mod-audio/cc-hw-arduino-shield/cases/distance/mod-arduino-shield-case-distance.sch

## KiCad design cases/distance/mod-arduino-shield-case-distance.sch (2014-12-04)

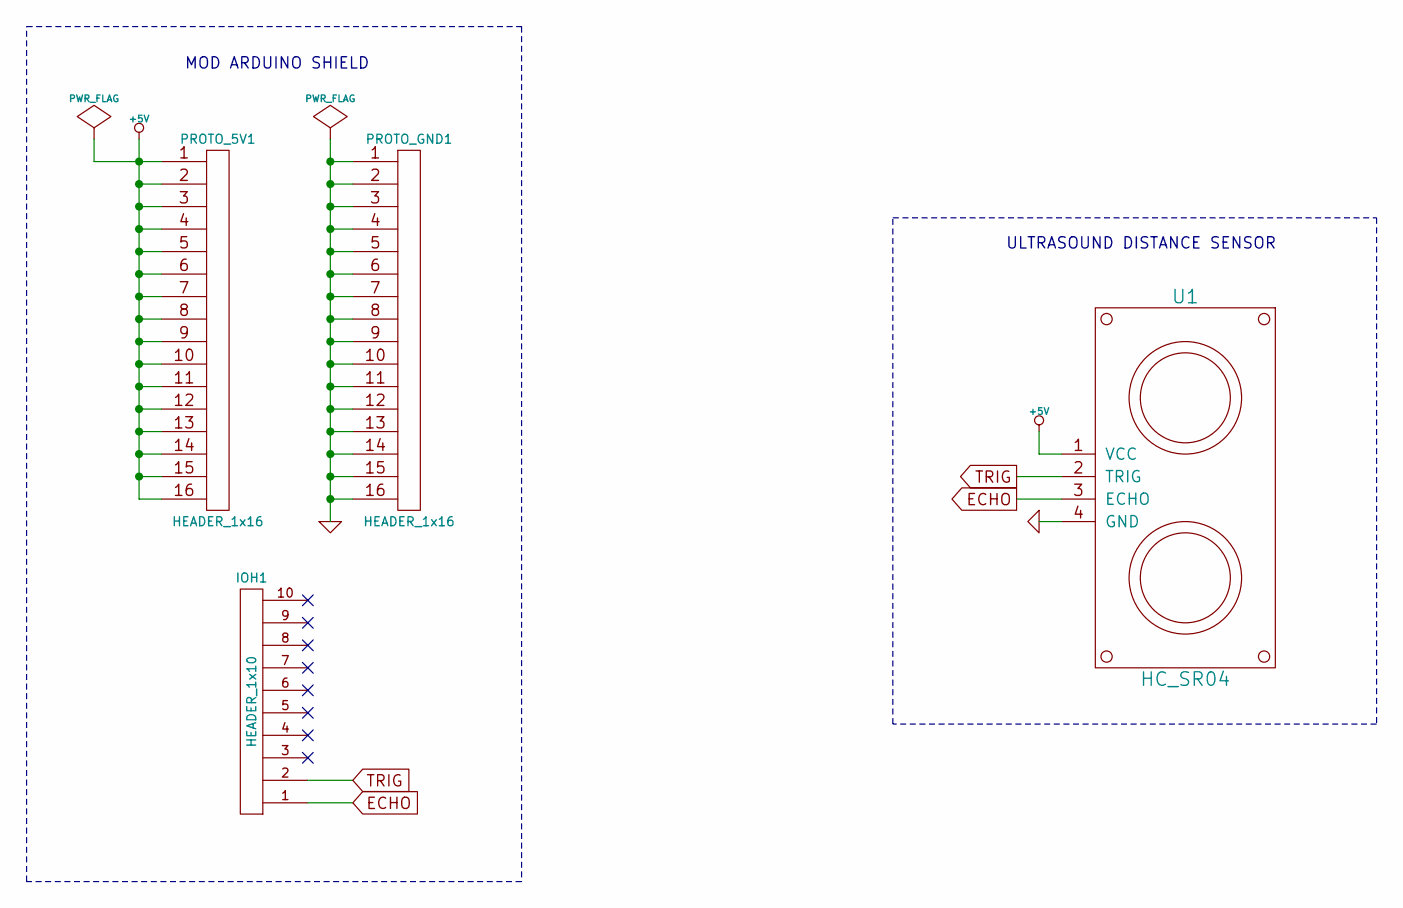
[picture p15: schematic mod-arduino-shield-case-distance.sch]

Parts:
IOH1: HEADER_1x10
PROTO_5V1: HEADER_1x16
PROTO_GND1: HEADER_1x16
U1: HC_SR04

Connections:
+5V: PROTO_5V1.1, PROTO_5V1.2, PROTO_5V1.3, PROTO_5V1.4, PROTO_5V1.5, PROTO_5V1.6, PROTO_5V1.7, PROTO_5V1.8, PROTO_5V1.9, PROTO_5V1.10, PROTO_5V1.11, PROTO_5V1.12, PROTO_5V1.13, PROTO_5V1.14, PROTO_5V1.15, PROTO_5V1.16, U1.1 (VCC)
ECHO: IOH1.1, U1.3 (ECHO)
GND: PROTO_GND1.1, PROTO_GND1.2, PROTO_GND1.3, PROTO_GND1.4, PROTO_GND1.5, PROTO_GND1.6, PROTO_GND1.7, PROTO_GND1.8, PROTO_GND1.9, PROTO_GND1.10, PROTO_GND1.11, PROTO_GND1.12, PROTO_GND1.13, PROTO_GND1.14, PROTO_GND1.15, PROTO_GND1.16, U1.4 (GND)
TRIG: IOH1.2, U1.2 (TRIG)

Notes on the sheet:
ULTRASOUND DISTANCE SENSOR
MOD ARDUINO SHIELD
