mod-audio/cc-hw-arduino-shield/cases/expression-pedal/mod-arduino-shield-case-expression-pedal.sch

## KiCad design cases/expression-pedal/mod-arduino-shield-case-expression-pedal.sch (2014-12-04)

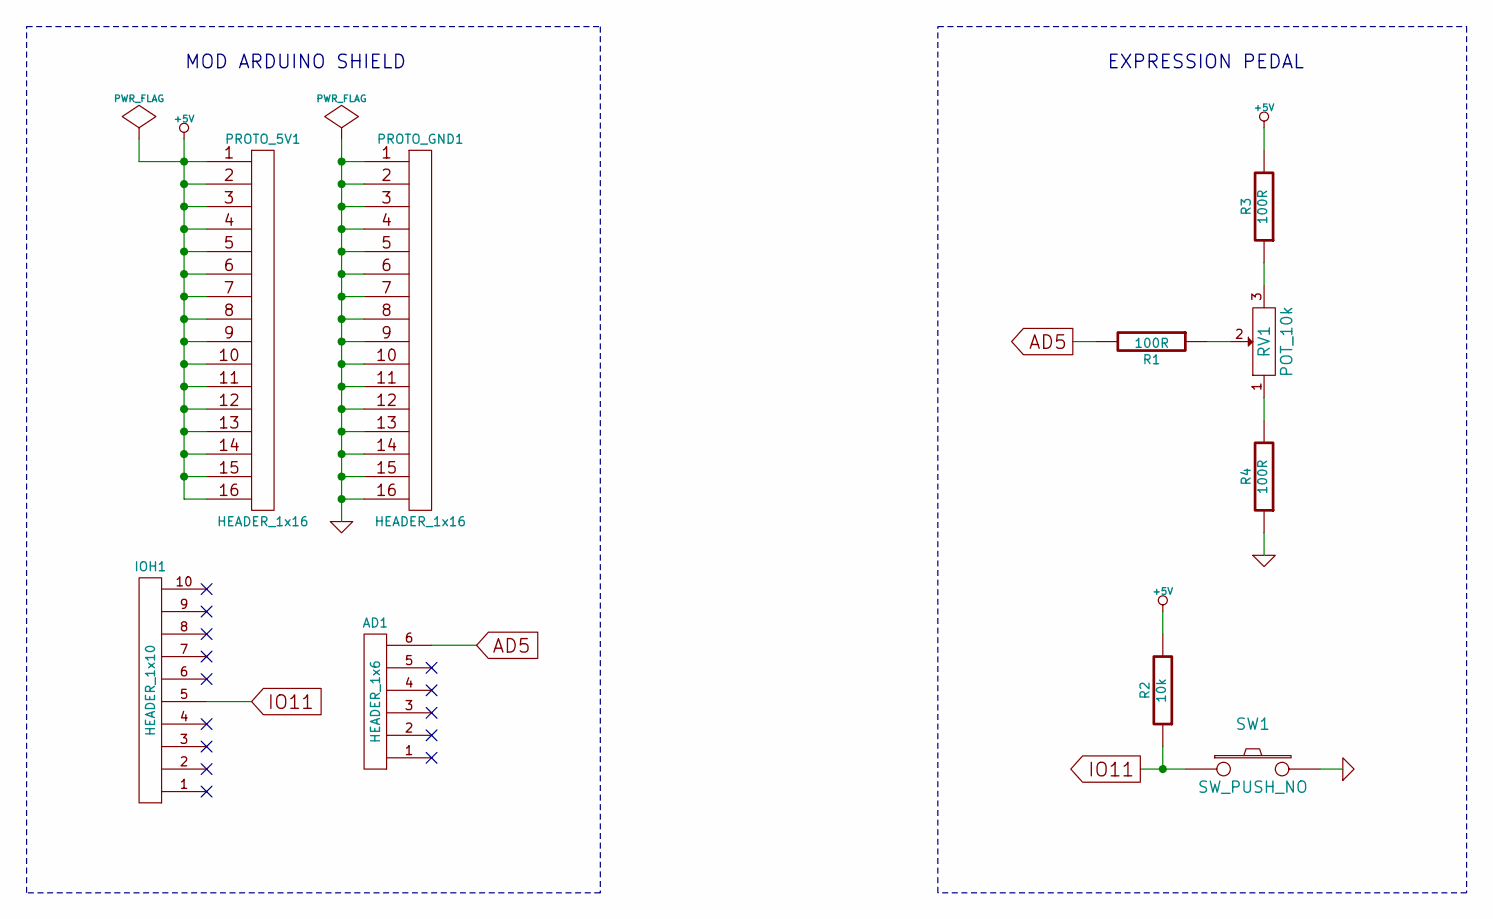
[picture p16: schematic mod-arduino-shield-case-expression-pedal.sch]

Parts:
AD1: HEADER_1x6
IOH1: HEADER_1x10
PROTO_5V1: HEADER_1x16
PROTO_GND1: HEADER_1x16
R1, R3, R4: 100R
R2: 10k
RV1: POT_10k
SW1: SW_PUSH_NO

Connections:
+5V: PROTO_5V1.1, PROTO_5V1.2, PROTO_5V1.3, PROTO_5V1.4, PROTO_5V1.5, PROTO_5V1.6, PROTO_5V1.7, PROTO_5V1.8, PROTO_5V1.9, PROTO_5V1.10, PROTO_5V1.11, PROTO_5V1.12, PROTO_5V1.13, PROTO_5V1.14, PROTO_5V1.15, PROTO_5V1.16, R2.2, R3.2
AD5: AD1.6, R1.2
GND: PROTO_GND1.1, PROTO_GND1.2, PROTO_GND1.3, PROTO_GND1.4, PROTO_GND1.5, PROTO_GND1.6, PROTO_GND1.7, PROTO_GND1.8, PROTO_GND1.9, PROTO_GND1.10, PROTO_GND1.11, PROTO_GND1.12, PROTO_GND1.13, PROTO_GND1.14, PROTO_GND1.15, PROTO_GND1.16, R4.1, SW1.2
IO11: IOH1.5, R2.1, SW1.1
unnamed: R1.1, RV1.2
unnamed: R3.1, RV1.3
unnamed: R4.2, RV1.1

Notes on the sheet:
MOD ARDUINO SHIELD
EXPRESSION PEDAL
