mod-audio/cc-hw-arduino-shield/cases/footswitch/mod-arduino-shield-case-footswitch.sch

## KiCad design cases/footswitch/mod-arduino-shield-case-footswitch.sch (2014-12-04)

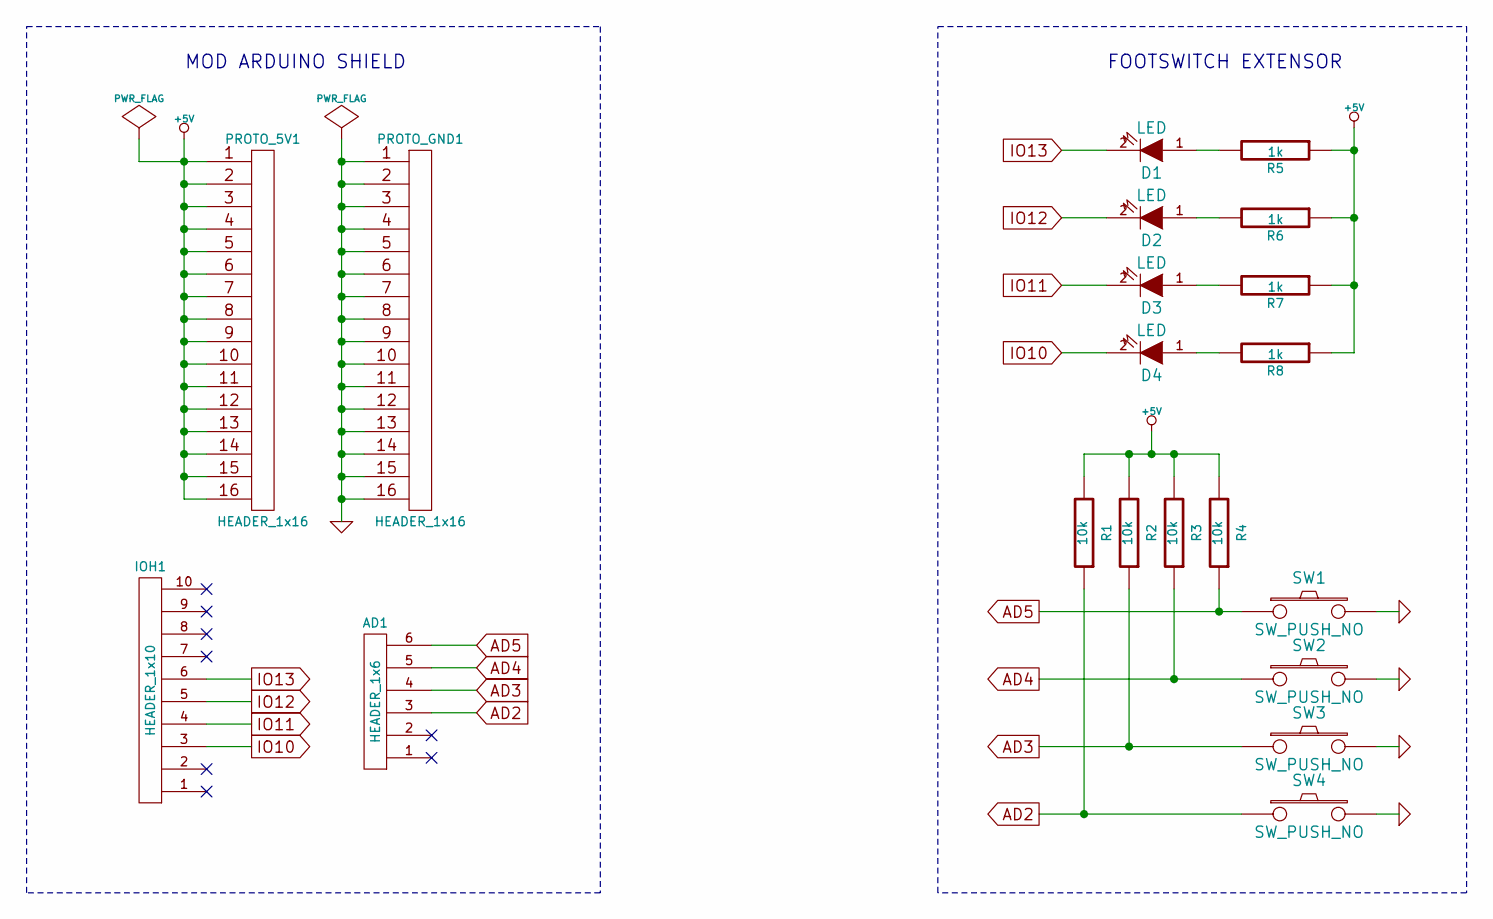
[picture p17: schematic mod-arduino-shield-case-footswitch.sch]

Parts:
AD1: HEADER_1x6
D1, D2, D3, D4: LED
IOH1: HEADER_1x10
PROTO_5V1: HEADER_1x16
PROTO_GND1: HEADER_1x16
R1, R2, R3, R4: 10k
R5, R6, R7, R8: 1k
SW1, SW2, SW3, SW4: SW_PUSH_NO

Connections:
+5V: PROTO_5V1.1, PROTO_5V1.2, PROTO_5V1.3, PROTO_5V1.4, PROTO_5V1.5, PROTO_5V1.6, PROTO_5V1.7, PROTO_5V1.8, PROTO_5V1.9, PROTO_5V1.10, PROTO_5V1.11, PROTO_5V1.12, PROTO_5V1.13, PROTO_5V1.14, PROTO_5V1.15, PROTO_5V1.16, R1.2, R2.2, R3.2, R4.2, R5.1, R6.1, R7.1, R8.1
AD2: AD1.3, R1.1, SW4.1
AD3: AD1.4, R2.1, SW3.1
AD4: AD1.5, R3.1, SW2.1
AD5: AD1.6, R4.1, SW1.1
GND: PROTO_GND1.1, PROTO_GND1.2, PROTO_GND1.3, PROTO_GND1.4, PROTO_GND1.5, PROTO_GND1.6, PROTO_GND1.7, PROTO_GND1.8, PROTO_GND1.9, PROTO_GND1.10, PROTO_GND1.11, PROTO_GND1.12, PROTO_GND1.13, PROTO_GND1.14, PROTO_GND1.15, PROTO_GND1.16, SW1.2, SW2.2, SW3.2, SW4.2
IO10: D4.2 (K), IOH1.3
IO11: D3.2 (K), IOH1.4
IO12: D2.2 (K), IOH1.5
IO13: D1.2 (K), IOH1.6
unnamed: D1.1 (A), R5.2
unnamed: D2.1 (A), R6.2
unnamed: D3.1 (A), R7.2
unnamed: D4.1 (A), R8.2

Notes on the sheet:
MOD ARDUINO SHIELD
FOOTSWITCH EXTENSOR
