mod-audio/cc-hw-arduino-shield/cases/ldr/mod-arduino-shield-case-ldr.sch

## KiCad design cases/ldr/mod-arduino-shield-case-ldr.sch (2014-12-04)

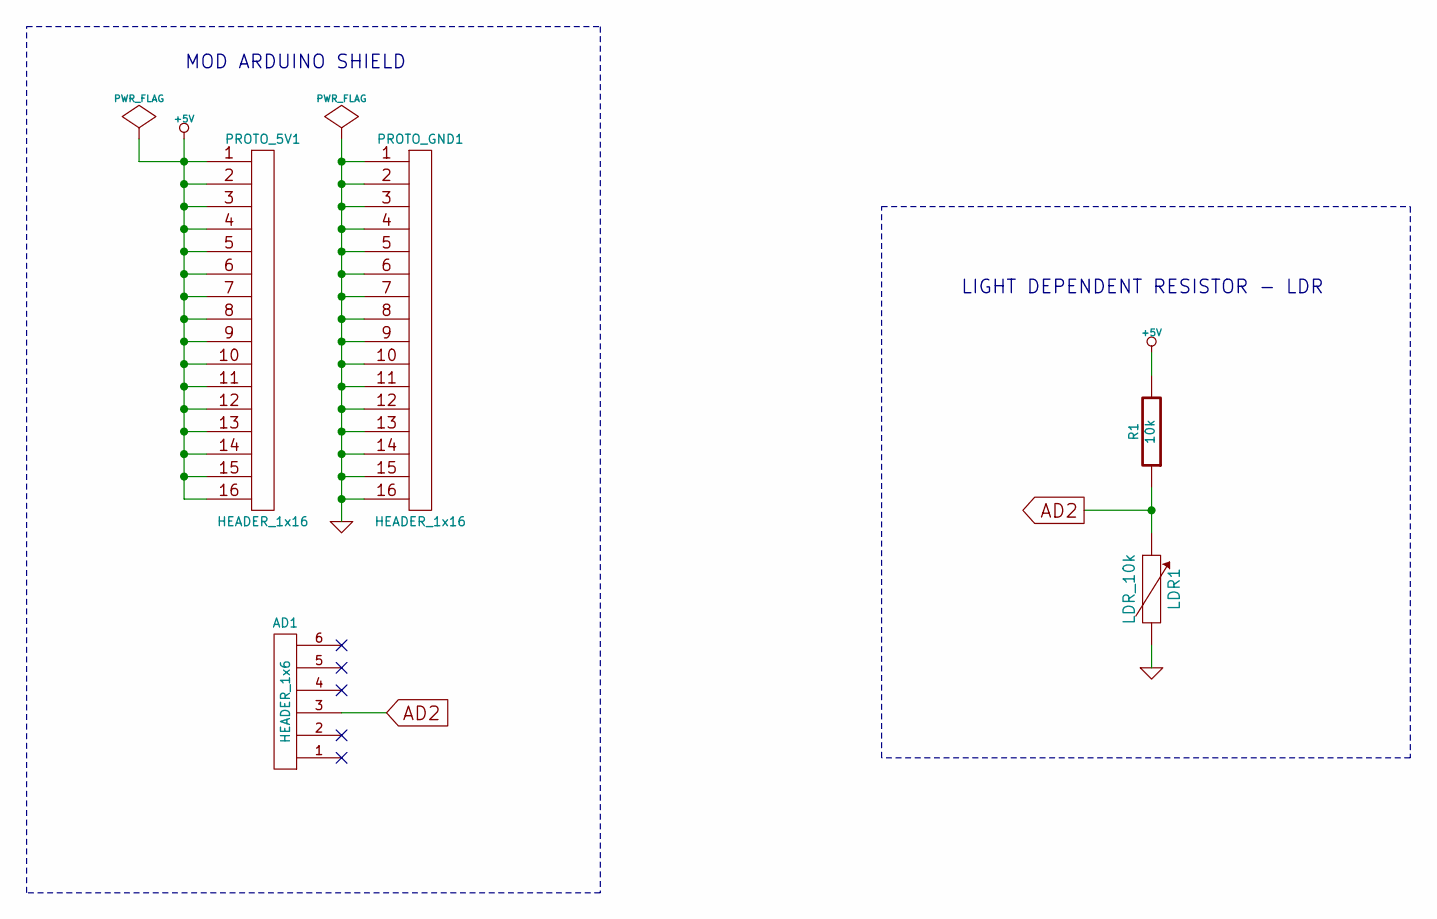
[picture p18: schematic mod-arduino-shield-case-ldr.sch]

Parts:
AD1: HEADER_1x6
LDR1: LDR_10k
PROTO_5V1: HEADER_1x16
PROTO_GND1: HEADER_1x16
R1: 10k

Connections:
+5V: PROTO_5V1.1, PROTO_5V1.2, PROTO_5V1.3, PROTO_5V1.4, PROTO_5V1.5, PROTO_5V1.6, PROTO_5V1.7, PROTO_5V1.8, PROTO_5V1.9, PROTO_5V1.10, PROTO_5V1.11, PROTO_5V1.12, PROTO_5V1.13, PROTO_5V1.14, PROTO_5V1.15, PROTO_5V1.16, R1.2
AD2: AD1.3, LDR1.1, R1.1
GND: LDR1.2, PROTO_GND1.1, PROTO_GND1.2, PROTO_GND1.3, PROTO_GND1.4, PROTO_GND1.5, PROTO_GND1.6, PROTO_GND1.7, PROTO_GND1.8, PROTO_GND1.9, PROTO_GND1.10, PROTO_GND1.11, PROTO_GND1.12, PROTO_GND1.13, PROTO_GND1.14, PROTO_GND1.15, PROTO_GND1.16

Notes on the sheet:
MOD ARDUINO SHIELD
LIGHT DEPENDENT RESISTOR - LDR
